mlab-modules/LION1CELL02/doc/gen/dxf/LION1CELL02-B_Fab.dxf

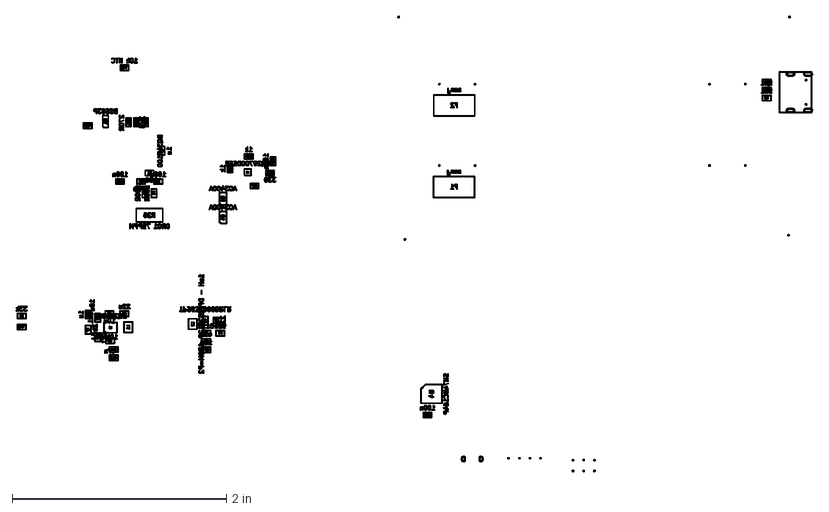
[picture p15: CAD file, 2026-05-15]
doc/gen/dxf/LION1CELL02-B_Fab.dxf
7.44 x 4.25 in
