mlab-modules/LION1CELL02/doc/gen/dxf/LION1CELL02-F_Fab.dxf

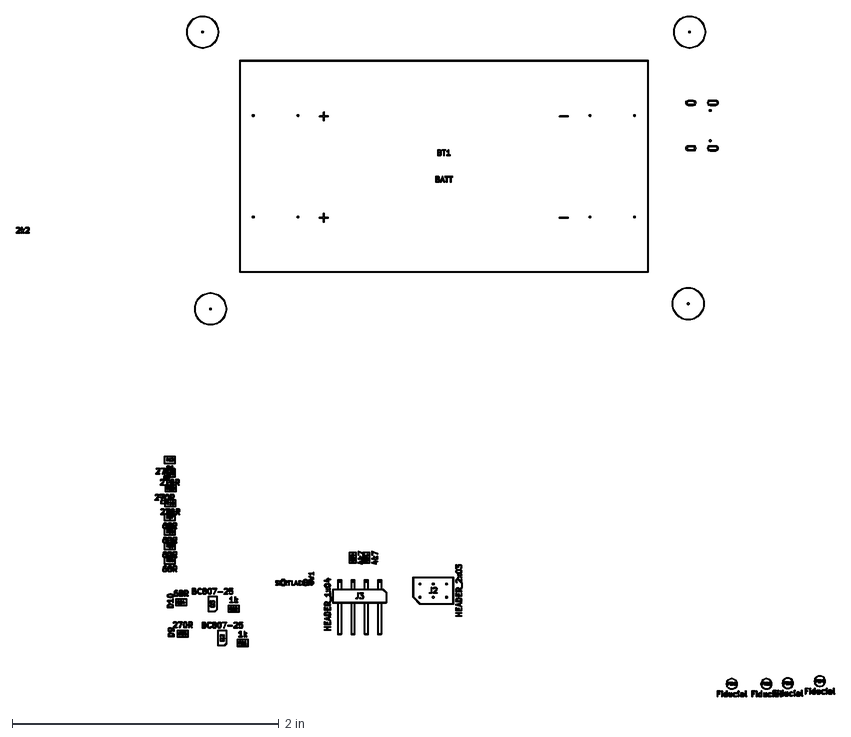
[picture p16: CAD file, 2026-05-15]
doc/gen/dxf/LION1CELL02-F_Fab.dxf
6.14 x 5.11 in
