mlab-modules/LION1CELL02/doc/gen/dxf/LION1CELL02-F_Courtyard.dxf

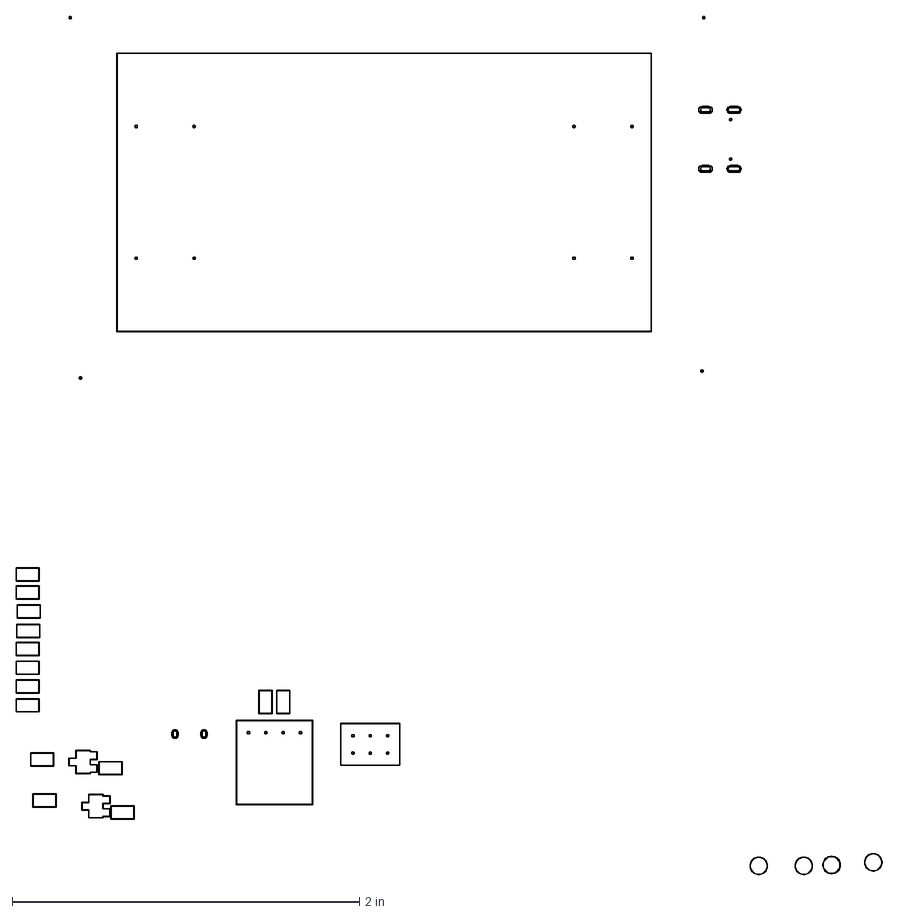
[picture p17: CAD file, 2026-05-15]
doc/gen/dxf/LION1CELL02-F_Courtyard.dxf
4.99 x 4.95 in
